ddB0515/epdInky/examples/epd/FastJsonBasic/main/main.cpp

// FastJsonDL — basic usage example
//
// Demonstrates how to initialise the EPD panel, build a JSON layout, register
// custom fonts, and render everything using FastJsonDL.
//
// Target board : M5Paper S3 (ESP32-S3) — change BB_PANEL_M5PAPERS3 and the
//                font pointers to match your own hardware / font set.

#include <stdio.h>
#include "FastEPD.h"
#include "FastJsonDL.h"

// ---------------------------------------------------------------------------
// Font data — MUST be replaced with a real font generated by the FastEPD
// fontconvert tool (see FastEPD/fontconvert/README.md).
//
// To generate Ubuntu40.h from a TTF file:
//   ./fontconvert Ubuntu.ttf 40 > Ubuntu40.h
// Then #include "Ubuntu40.h" and remove the extern declaration below.
//
// Without valid font data the drawString item will produce no visible output.
// ---------------------------------------------------------------------------
#include "ubuntu30.h"
#include "ubuntu40.h"

// Font registry: maps JSON "font" field values to in-memory font data.
static const FastJsonDLFont fonts[] = {
    { "Ubuntu30", ubuntu30 },
    { "Ubuntu40", ubuntu40 },
};

// ---------------------------------------------------------------------------
// JSON layout
// ---------------------------------------------------------------------------
// Creative 4BPP demo layout:
// - Force 4BPP (0..15 greyscale) and clear to white.
// - Build simple layered shapes and lines.
// - Render multiple text colors to make grayscale differences obvious.
//
// NOTE — y coordinate for drawString:
// When a BB-format font is loaded (as produced by FastEPD fontconvert), the y
// value is the TEXT BASELINE, not the top-left of the glyph.  Ubuntu40 has an
// ascender height of approximately 50 pixels, so the glyph top sits at
// (y - 50).  Using "y": 10 would place the top of the characters at y = -40,
// entirely off-screen and silently invisible.  Always set y >= font ascender.
static const char LAYOUT_JSON[] = R"({
  "display_bpp": 1,
  "clear": true,
  "items": [
    {
      "type": "fillRect",
      "x": 210,
      "y": 500,
      "w": 340,
      "h": 100,
      "c": 0
    },
    {
      "type": "drawString",
      "font": "Ubuntu40",
      "string": "Hello from FastJSON demo!",
      "x": 38,
      "y": 98,
      "c": 0
    },
    {
      "type": "fillCircle",
      "x": 118,
      "y": 300,
      "r": 80,
      "c": 10
    },
    {
      "type": "fillRect",
      "x": 718,
      "y": 300,
      "w": 200,
      "h": 700,
      "c": 6
    },
    {
      "type": "drawString",
      "font": "Ubuntu40",
      "string": "and another text",
      "x": 220,
      "y": 198,
      "c": 15
    }
  ]
})";

// ---------------------------------------------------------------------------
// app_main
// ---------------------------------------------------------------------------

// Using heap-allocated pointers avoids a Store access fault on RISC-V targets
// (e.g. ESP32-C5) where constructing a large C++ object in BSS/static storage
// inside app_main() can crash inside bbepInitPanel().  This matches the
// lifecycle used in production C5 firmware.
static FASTEPD      *epaper = nullptr;
static FastJsonDL   *dl     = nullptr;

extern "C" void app_main(void)
{
    // Allocate the EPD driver on the heap.
    epaper = new FASTEPD();

    // Initialise the panel.  Replace BB_PANEL_M5PAPERS3 with the constant
    // that matches your hardware (see the BB_PANEL_* enum in FastEPD.h).
    int rc = epaper->initPanel(BB_PANEL_EPDINKY_P4_16);
    if (rc != BBEP_SUCCESS) {
        printf("EPD init failed (%d)\n", rc);
        return;
    }
    // Optional: override the active pixel area and apply mirror/rotation flags.
    // Remove or adjust for your panel dimensions and orientation.
    epaper->setPanelSize(1264, 1680, BB_PANEL_FLAG_NONE, -1400);

    // Optional: override the active pixel area and apply mirror/rotation flags.
    // Remove or adjust for your panel dimensions and orientation.
    // epaper->setPanelSize(EPD_WIDTH, EPD_HEIGHT, BB_PANEL_FLAG_MIRROR_X);

    // Optional: select the rendering bit-depth.
    //   BB_MODE_1BPP — 1-bit black/white (fastest update)
    //   BB_MODE_2BPP — 4 grey levels
    //   BB_MODE_4BPP — 16 grey levels (set "display_bpp": 4 in JSON too)
    epaper->setMode(BB_MODE_1BPP);

    // Build the renderer on the heap and register the font table.
    dl = new FastJsonDL(*epaper);
    dl->setFontRegistry(fonts, sizeof(fonts) / sizeof(fonts[0]));

    // Render the JSON layout.
    printf("FastJsonDL: rendering layout...\n");
    if (!dl->renderJsonString(LAYOUT_JSON)) {
        printf("FastJsonDL error: %s\n", dl->getLastError());
        return;
    }
    printf("FastJsonDL: render OK, updating panel\n");

    // Push the frame buffer to the physical display.
    epaper->fullUpdate();
}
