ddB0515/epdInky/examples/epd/calendar/main/sd_card_functions.c

#include <string.h>

#include "esp_err.h"
#include "esp_log.h"
#include "esp_vfs_fat.h"
#include "driver/gpio.h"
#include "driver/sdmmc_host.h"
#include "sdmmc_cmd.h"
#include "freertos/FreeRTOS.h"
#include "esp_idf_version.h"

#if SOC_SDMMC_IO_POWER_EXTERNAL
#include "sd_pwr_ctrl_by_on_chip_ldo.h"
#endif

#include "sd_card_functions.h"

/**
 * On ESP-IDF master branch, the sdmmc host controller can only be initialised once
 *
 * This workaround ensures that either ESP-Hosted (if using SDIO as the transport) or
 * the SD Card Example will initialise the sdmmc host control
 *
 * See the `README.md` for more details.
 */
#if CONFIG_ESP_HOSTED_SDIO_HOST_INTERFACE && (ESP_IDF_VERSION >= ESP_IDF_VERSION_VAL(6, 0, 0))
#define WORKAROUND_HOSTED_DOES_SDMMC_HOST_INIT 1
#else
#define WORKAROUND_HOSTED_DOES_SDMMC_HOST_INIT 0
#endif

static const char *TAG = "sd_card_fns";

static sdmmc_card_t *card = NULL;
static sd_pwr_ctrl_handle_t pwr_ctrl_handle = NULL;

esp_err_t sd_card_write_file(const char *path, char *data)
{
    ESP_LOGI(TAG, "Opening file %s", path);
    FILE *f = fopen(path, "w");
    if (f == NULL) {
        ESP_LOGE(TAG, "Failed to open file for writing");
        return ESP_FAIL;
    }
    fprintf(f, data);
    fclose(f);
    ESP_LOGI(TAG, "File written");

    return ESP_OK;
}

esp_err_t sd_card_read_file(const char *path)
{
    ESP_LOGI(TAG, "Reading file %s", path);
    FILE *f = fopen(path, "r");
    if (f == NULL) {
        ESP_LOGE(TAG, "Failed to open file for reading");
        return ESP_FAIL;
    }
    char line[EXAMPLE_MAX_CHAR_SIZE];
    fgets(line, sizeof(line), f);
    fclose(f);

    // strip newline
    char *pos = strchr(line, '\n');
    if (pos) {
        *pos = '\0';
    }
    ESP_LOGI(TAG, "Read from file: '%s'", line);

    return ESP_OK;
}

#if CONFIG_EXAMPLE_PIN_CARD_POWER_RESET
esp_err_t sd_card_reset_card_power(void)
{
    esp_err_t ret = ESP_FAIL;
    gpio_config_t io_conf = {
        .mode = GPIO_MODE_OUTPUT,
        .pin_bit_mask = (1ULL<<CONFIG_EXAMPLE_PIN_CARD_POWER_RESET),
    };
    ret = gpio_config(&io_conf);
    if (ret != ESP_OK) {
        ESP_LOGE(TAG, "Failed to config GPIO");
        return ret;
    }

    ret = gpio_set_level(CONFIG_EXAMPLE_PIN_CARD_POWER_RESET, 1);
    if (ret != ESP_OK) {
        ESP_LOGE(TAG, "Failed to set GPIO level");
        return ret;
    }

    vTaskDelay(100 / portTICK_PERIOD_MS);

    ret = gpio_set_level(CONFIG_EXAMPLE_PIN_CARD_POWER_RESET, 0);
    if (ret != ESP_OK) {
        ESP_LOGE(TAG, "Failed to set GPIO level");
        return ret;
    }

    return ESP_OK;
}
#endif // CONFIG_EXAMPLE_PIN_CARD_POWER_RESET

char * sd_card_get_card_name(void)
{
    if (card) {
        return card->cid.name;
    } else {
        return NULL;
    }
}

static esp_err_t sdmmc_host_init_dummy(void)
{
    return ESP_OK;
}

static esp_err_t sdmmc_host_deinit_dummy(void)
{
    return ESP_OK;
}

esp_err_t sd_card_mount(int slot, const char * mount_point)
{
    esp_err_t ret;

    if (!mount_point) {
        ESP_LOGE(TAG, "No mount point provided");
        return ESP_FAIL;
    }

#if CONFIG_IDF_TARGET_ESP32P4
    // on ESP32-P4 Dev Board, the SDCard is on SDMMC Slot 0
    // ESP-Hosted uses SDMMC Slot 1
    if (slot != SDMMC_HOST_SLOT_0) {
        ESP_LOGE(TAG, "For ESP32-P4, SD Card slot should be SDMMC_HOST_SLOT_0");
        return ESP_FAIL;
    }
#endif

    // Options for mounting the filesystem.
    esp_vfs_fat_sdmmc_mount_config_t mount_config = {
        .format_if_mount_failed = false,
        .max_files = 5,
        .allocation_unit_size = 16 * 1024
    };
    ESP_LOGI(TAG, "Initializing SD card");

    // Use settings defined above to initialize SD card and mount FAT filesystem.
    // Note: esp_vfs_fat_sdmmc/sdspi_mount is all-in-one convenience functions.
    // Please check its source code and implement error recovery when developing
    // production applications.

    ESP_LOGI(TAG, "Using SDMMC peripheral");

    // By default, SD card frequency is initialized to SDMMC_FREQ_DEFAULT (20MHz)
    // For setting a specific frequency, use host.max_freq_khz (range 400kHz - 40MHz for SDMMC)
    // Example: for fixed frequency of 10MHz, use host.max_freq_khz = 10000;
    sdmmc_host_t host = SDMMC_HOST_DEFAULT();
    host.slot = slot;
    host.init = &sdmmc_host_init_dummy;
    host.deinit = &sdmmc_host_deinit_dummy;


    // For SoCs where the SD power can be supplied both via an internal or external (e.g. on-board LDO) power supply.
    // When using specific IO pins (which can be used for ultra high-speed SDMMC) to connect to the SD card
    // and the internal LDO power supply, we need to initialize the power supply first.
#if CONFIG_EXAMPLE_SD_PWR_CTRL_LDO_INTERNAL_IO
    sd_pwr_ctrl_ldo_config_t ldo_config = {
        .ldo_chan_id = CONFIG_EXAMPLE_SD_PWR_CTRL_LDO_IO_ID,
    };

    ret = sd_pwr_ctrl_new_on_chip_ldo(&ldo_config, &pwr_ctrl_handle);
    if (ret != ESP_OK) {
        ESP_LOGE(TAG, "Failed to create a new on-chip LDO power control driver");
        return ret;
    }
    host.pwr_ctrl_handle = pwr_ctrl_handle;
#endif

#if CONFIG_EXAMPLE_PIN_CARD_POWER_RESET
    ESP_ERROR_CHECK(sd_card_reset_card_power());
#endif

    // This initializes the slot without card detect (CD) and write protect (WP) signals.
    // Modify slot_config.gpio_cd and slot_config.gpio_wp if your board has these signals.
    sdmmc_slot_config_t slot_config = SDMMC_SLOT_CONFIG_DEFAULT();
    slot_config.width = 4;
    slot_config.clk = CONFIG_EXAMPLE_PIN_CLK;
    slot_config.cmd = CONFIG_EXAMPLE_PIN_CMD;
    slot_config.d0 = CONFIG_EXAMPLE_PIN_D0;
    slot_config.d1 = CONFIG_EXAMPLE_PIN_D1;
    slot_config.d2 = CONFIG_EXAMPLE_PIN_D2;
    slot_config.d3 = CONFIG_EXAMPLE_PIN_D3;
    slot_config.flags |= SDMMC_SLOT_FLAG_INTERNAL_PULLUP;

    ESP_LOGI(TAG, "Mounting filesystem");
    ret = esp_vfs_fat_sdmmc_mount(mount_point, &host, &slot_config, &mount_config, &card);

    if (ret != ESP_OK) {
        if (ret == ESP_FAIL) {
            ESP_LOGE(TAG, "Failed to mount filesystem. ");
        } else {
            ESP_LOGE(TAG, "Failed to initialize the card (%s). "
                     "Make sure SD card lines have pull-up resistors in place.", esp_err_to_name(ret));
        }
        return ret;
    }

    ESP_LOGI(TAG, "Filesystem mounted");

    // Card has been initialized, print its properties
    sdmmc_card_print_info(stdout, card);

    return ESP_OK;
}

esp_err_t sd_card_unmount(const char * mount_point)
{
    esp_err_t ret;

    if (!mount_point) {
        ESP_LOGE(TAG, "No mount point provided");
        return ESP_FAIL;
    }

    if (card) {
        esp_vfs_fat_sdcard_unmount(mount_point, card);

        // Deinitialize the power control driver if it was used
#if CONFIG_EXAMPLE_SD_PWR_CTRL_LDO_INTERNAL_IO
        if (pwr_ctrl_handle) {
            ret = sd_pwr_ctrl_del_on_chip_ldo(pwr_ctrl_handle);
            if (ret != ESP_OK) {
                ESP_LOGE(TAG, "Failed to delete the on-chip LDO power control driver");
                return ret;
            }
        }
#endif
        return ESP_OK;
    } else {
        ESP_LOGE(TAG, "no SD Card mounted: cannot unmount");
        return ESP_FAIL;
    }
}
